milovanpms/tictac/assets/images/block_diagram.png

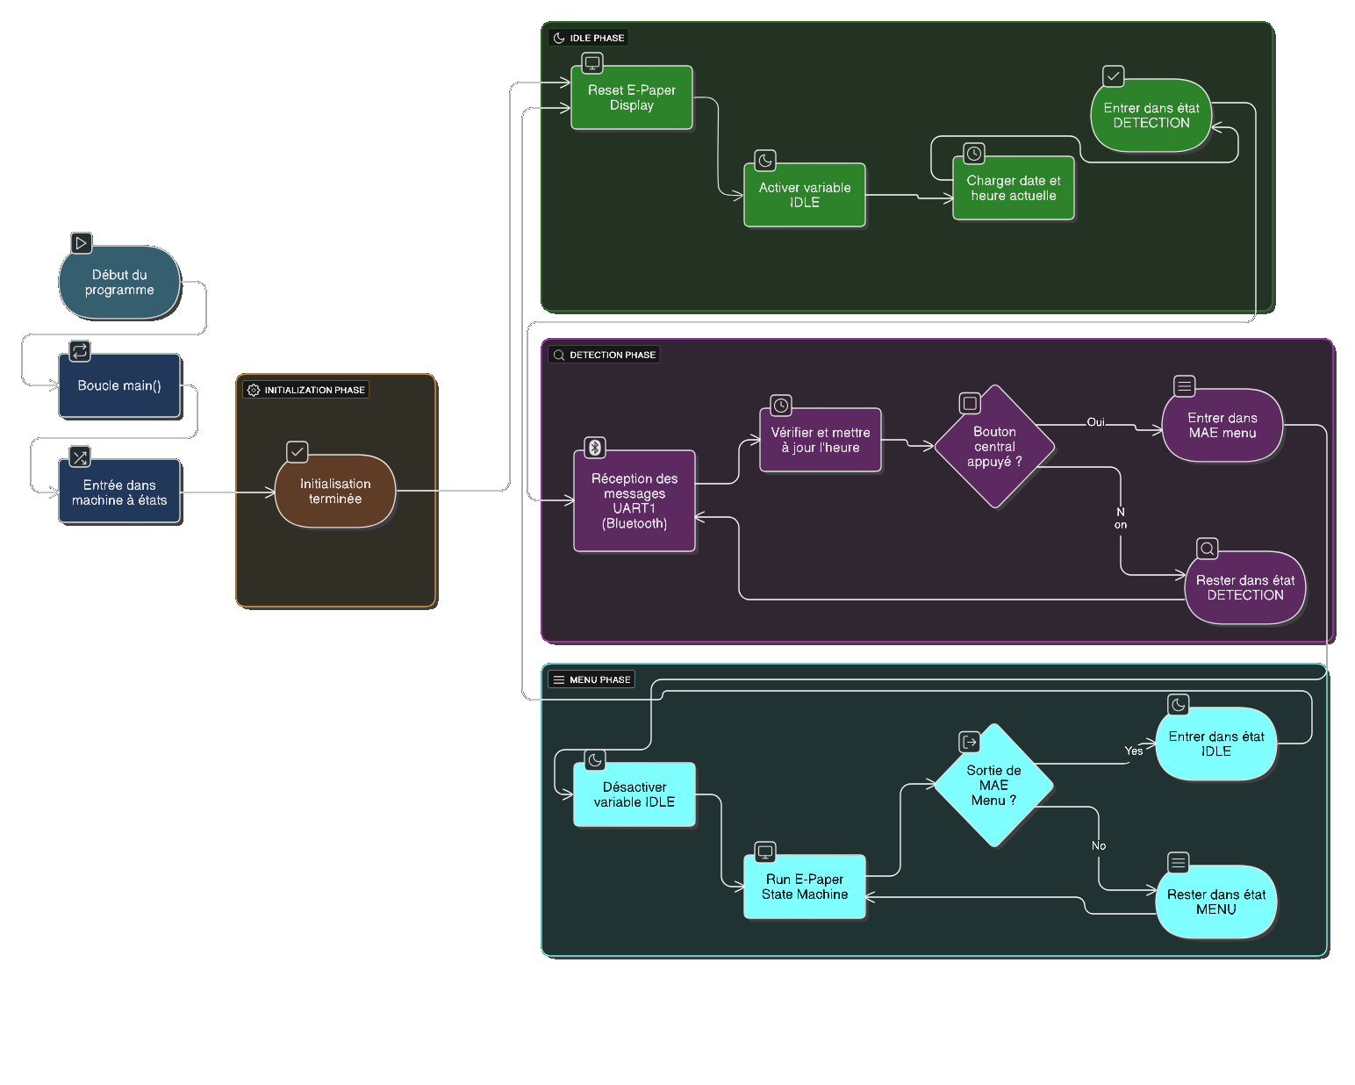
assets/images/block_diagram.png
