milovanpms/tictac/assets/images/croquis.jpg

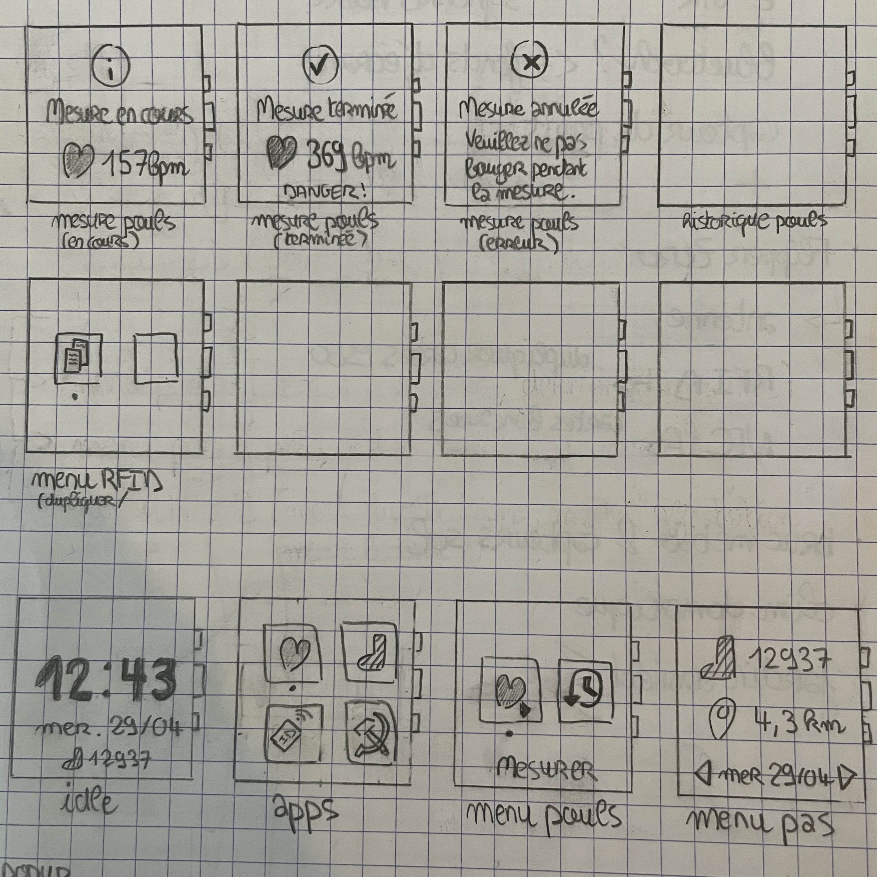
assets/images/croquis.jpg
