milovanpms/tictac/assets/images/photos/IMG_0963.jpg

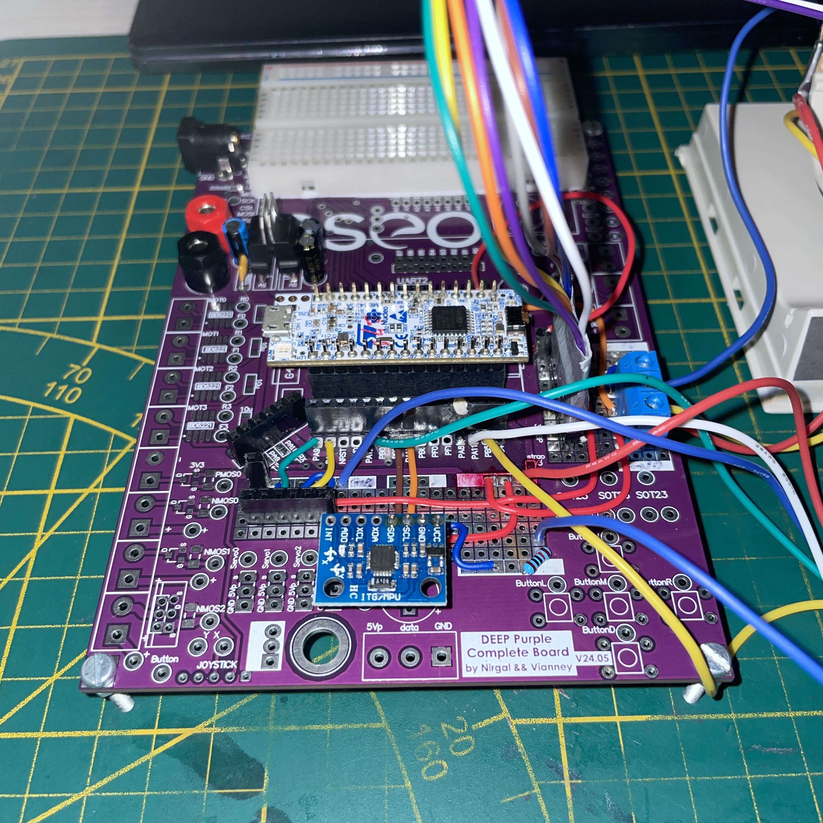
assets/images/photos/IMG_0963.jpg
