milovanpms/tictac/assets/images/photos/IMG_0964.jpg

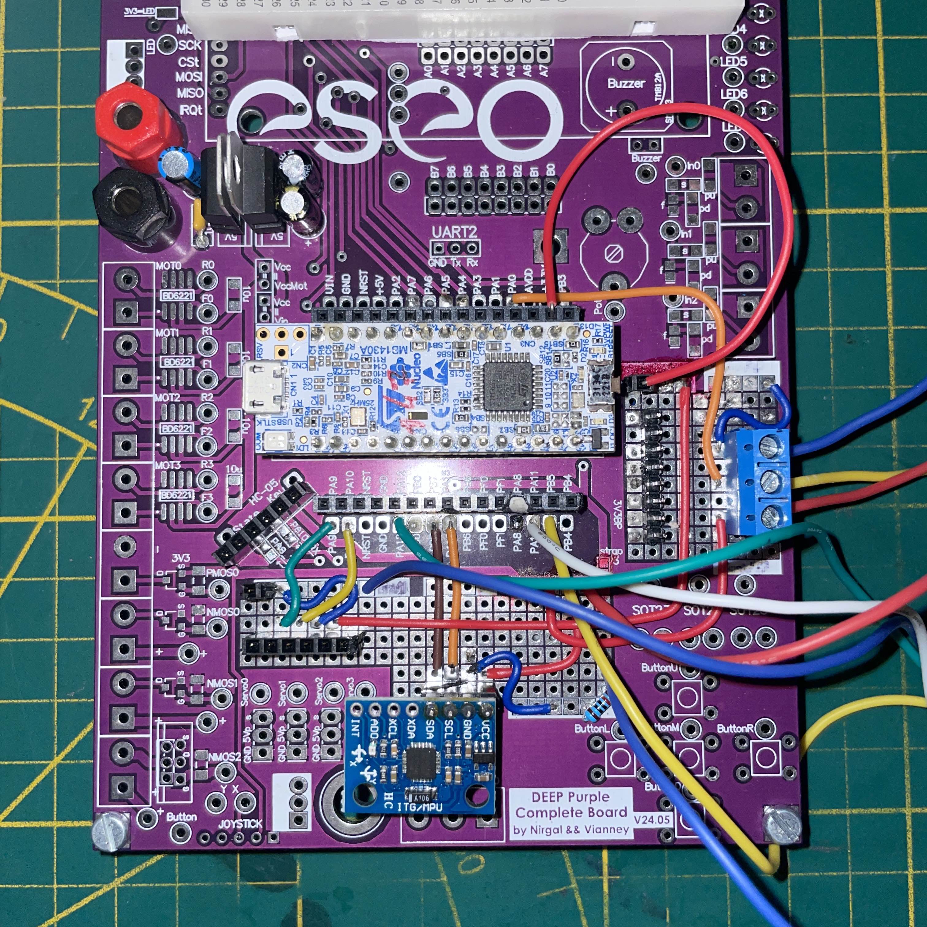
assets/images/photos/IMG_0964.jpg
