milovanpms/tictac/assets/images/photos/IMG_0965.jpg

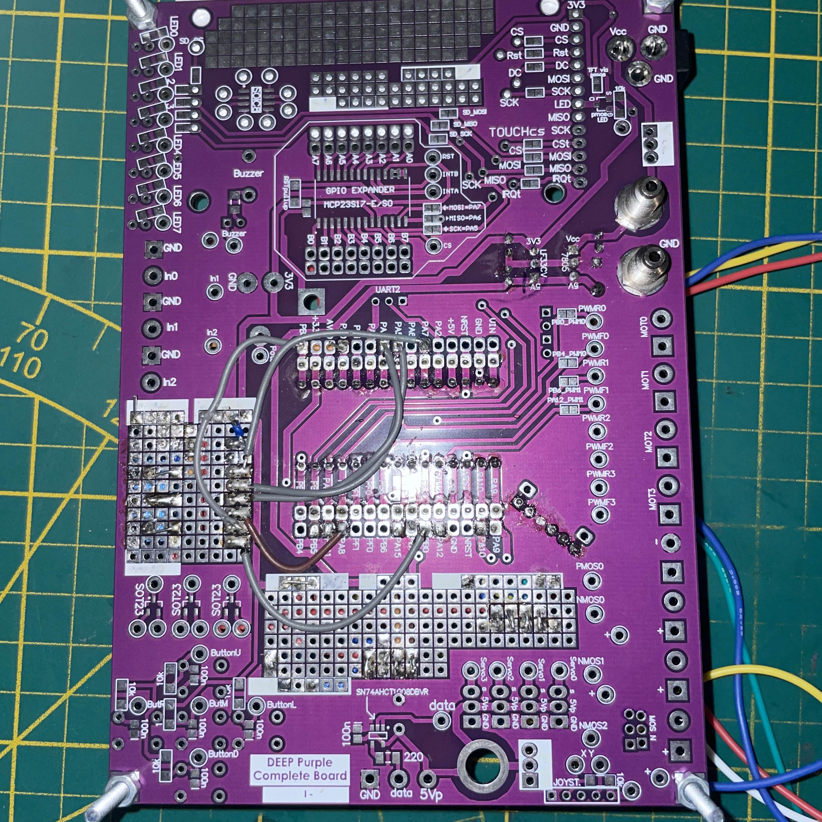
assets/images/photos/IMG_0965.jpg
