milovanpms/tictac/firmware/app/epaper/epaper_bitmaps.h

/**
 * @file epaper_bitmaps.h
 * @author Milovan Paget
 * @brief Définition des données bitmap pour l'affichage des icônes
 */

#include <stdlib.h>

extern const unsigned char image[];

/**
 * @brief Tableau de données bitmap pour l'icône cadre
 *
 */
static const uint8_t cadre[343] = {
    // ∙∙∙∙∙∙∙∙∙∙∙∙∙∙∙∙∙∙∙∙∙∙∙∙∙∙∙∙∙∙∙∙∙∙∙∙∙∙∙∙∙∙∙∙∙∙∙∙∙
    // ∙∙∙∙∙∙∙∙∙∙∙∙∙∙∙∙∙∙∙∙∙∙∙∙∙∙∙∙∙∙∙∙∙∙∙∙∙∙∙∙∙∙∙∙∙∙∙∙∙
    // ∙∙∙∙∙∙∙∙∙∙∙∙∙∙∙∙∙∙█████████████∙∙∙∙∙∙∙∙∙∙∙∙∙∙∙∙∙∙
    // ∙∙∙∙∙∙∙∙∙∙∙∙∙∙∙∙∙∙█████████████∙∙∙∙∙∙∙∙∙∙∙∙∙∙∙∙∙∙
    // ∙∙∙∙∙∙∙∙∙∙∙∙∙∙█████████████████████∙∙∙∙∙∙∙∙∙∙∙∙∙∙
    // ∙∙∙∙∙∙∙∙∙∙∙∙∙∙█████████████████████∙∙∙∙∙∙∙∙∙∙∙∙∙∙
    // ∙∙∙∙∙∙∙∙∙∙█████████∙∙∙∙∙∙∙∙∙∙∙█████████∙∙∙∙∙∙∙∙∙∙
    // ∙∙∙∙∙∙∙∙∙∙█████████∙∙∙∙∙∙∙∙∙∙∙█████████∙∙∙∙∙∙∙∙∙∙
    // ∙∙∙∙∙∙∙∙██████████∙∙∙∙∙∙∙∙∙∙∙∙███████████∙∙∙∙∙∙∙∙
    // ∙∙∙∙∙∙∙∙███████∙∙∙∙∙∙∙∙∙∙∙∙∙∙∙∙∙∙∙███████∙∙∙∙∙∙∙∙
    // ∙∙∙∙∙∙████████∙∙∙∙∙∙∙∙∙∙∙∙∙∙∙∙∙∙∙∙█████████∙∙∙∙∙∙
    // ∙∙∙∙∙∙███████∙∙∙∙∙∙∙∙∙∙∙∙∙∙∙∙∙∙∙∙∙∙∙███████∙∙∙∙∙∙
    // ∙∙∙∙∙∙██████∙∙∙∙∙∙∙∙∙∙∙∙∙∙∙∙∙∙∙∙∙∙∙∙███████∙∙∙∙∙∙
    // ∙∙∙∙∙∙█████∙∙∙∙∙∙∙∙∙∙∙∙∙∙∙∙∙∙∙∙∙∙∙∙∙∙∙█████∙∙∙∙∙∙
    // ∙∙∙∙██████∙∙∙∙∙∙∙∙∙∙∙∙∙∙∙∙∙∙∙∙∙∙∙∙∙∙∙∙███████∙∙∙∙
    // ∙∙∙∙█████∙∙∙∙∙∙∙∙∙∙∙∙∙∙∙∙∙∙∙∙∙∙∙∙∙∙∙∙∙∙∙█████∙∙∙∙
    // ∙∙∙∙█████∙∙∙∙∙∙∙∙∙∙∙∙∙∙∙∙∙∙∙∙∙∙∙∙∙∙∙∙∙∙∙█████∙∙∙∙
    // ∙∙∙∙█████∙∙∙∙∙∙∙∙∙∙∙∙∙∙∙∙∙∙∙∙∙∙∙∙∙∙∙∙∙∙∙█████∙∙∙∙
    // ∙∙██████∙∙∙∙∙∙∙∙∙∙∙∙∙∙∙∙∙∙∙∙∙∙∙∙∙∙∙∙∙∙∙∙███████∙∙
    // ∙∙████∙∙∙∙∙∙∙∙∙∙∙∙∙∙∙∙∙∙∙∙∙∙∙∙∙∙∙∙∙∙∙∙∙∙∙∙█████∙∙
    // ∙∙████∙∙∙∙∙∙∙∙∙∙∙∙∙∙∙∙∙∙∙∙∙∙∙∙∙∙∙∙∙∙∙∙∙∙∙∙█████∙∙
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
    0xfc, 0x00, 0x00, 0x00, 0x00, 0x00, 0xfc,
    0xfc, 0x00, 0x00, 0x00, 0x00, 0x00, 0xfc,
    0xfc, 0x00, 0x00, 0x00, 0x00, 0x00, 0xfc,
    0xfc, 0x00, 0x00, 0x00, 0x00, 0x00, 0xfc,
    0xfc, 0x00, 0x00, 0x00, 0x00, 0x00, 0xfc,
    0xfc, 0x00, 0x00, 0x00, 0x00, 0x00, 0xfc,
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
};

/**
 * @brief Tableau de données bitmap pour l'icône satellite
 *
 */
static const uint8_t satellite[120] = {
    // ∙∙∙∙∙∙∙█████∙∙∙∙∙∙∙∙∙∙∙∙∙∙∙∙∙∙
    // ∙∙∙∙████████∙∙∙∙∙∙∙∙∙∙∙∙∙∙∙∙∙∙
    // ∙∙∙█████∙∙∙∙∙∙∙∙∙∙∙∙∙∙∙████∙∙∙
    // ∙∙███∙∙∙∙∙∙∙∙∙∙∙∙∙∙∙∙∙██████∙∙
    // ∙████∙∙███∙∙∙∙∙∙∙∙∙∙∙████████∙
    // ∙██∙∙█████∙∙∙∙∙∙∙∙∙∙██████████
    // ∙██∙∙███∙∙∙∙∙∙∙∙∙∙∙∙███∙██∙███
    // ███∙███∙∙∙█████∙∙∙████████████
    // ██∙∙██∙∙████████∙█████████████
    // ██∙∙██∙∙████∙∙██∙███∙██∙██∙███
    // ██∙∙∙∙∙███∙∙█████████████████∙
    // ██∙∙∙∙∙███∙██████████████████∙
    // ∙∙∙∙∙∙∙██∙██████∙███████████∙∙
    // ∙∙∙∙∙∙∙██∙█████∙∙∙████████∙∙∙∙
    // ∙∙∙∙∙∙∙████████∙∙∙████████∙∙∙∙
    // ∙∙∙∙∙∙∙∙█████∙∙∙∙∙∙∙█████∙∙∙∙∙
    // ∙∙∙∙∙∙∙∙∙∙██∙∙∙∙∙∙∙∙∙██∙∙∙∙∙∙∙
    // ∙∙∙∙∙∙∙∙█████∙∙∙∙∙∙∙∙████∙∙∙∙∙
    // ∙∙∙∙∙∙∙████████∙∙∙∙∙██████∙∙∙∙
    // ∙∙∙∙∙∙∙████████∙∙∙∙∙██∙∙██∙∙∙∙
    // ∙∙∙∙∙████∙██████∙∙∙∙∙██∙████∙∙
    // ∙∙∙∙██████████████∙∙∙███████∙∙
    // ∙∙∙████████████████∙∙███████∙∙
    // ∙∙████∙██∙██████∙██∙∙█████∙∙∙∙
    // ∙∙██████████████∙█████████∙∙∙∙
    // ∙∙█████████████∙∙∙███████∙∙∙∙∙
    // ∙∙████∙██∙███∙∙∙∙∙∙∙███∙∙∙∙∙∙∙
    // ∙∙∙██████████∙∙∙∙∙∙∙███∙∙∙∙∙∙∙
    // ∙∙∙∙████████∙∙∙∙∙∙∙∙∙∙∙∙∙∙∙∙∙∙
    // ∙∙∙∙∙█████∙∙∙∙∙∙∙∙∙∙∙∙∙∙∙∙∙∙∙∙
    0x01, 0xf0, 0x00, 0x00,
    0x0f, 0xf0, 0x00, 0x00,
    0x1f, 0x00, 0x01, 0xe0,
    0x38, 0x00, 0x03, 0xf0,
    0x79, 0xc0, 0x07, 0xf8,
    0x67, 0xc0, 0x0f, 0xfc,
    0x67, 0x00, 0x0e, 0xdc,
    0xee, 0x3e, 0x3f, 0xfc,
    0xcc, 0xff, 0x7f, 0xfc,
    0xcc, 0xf3, 0x76, 0xdc,
    0xc1, 0xcf, 0xff, 0xf8,
    0xc1, 0xdf, 0xff, 0xf8,
    0x01, 0xbf, 0x7f, 0xf0,
    0x01, 0xbe, 0x3f, 0xc0,
    0x01, 0xfe, 0x3f, 0xc0,
    0x00, 0xf8, 0x0f, 0x80,
    0x00, 0x30, 0x06, 0x00,
    0x00, 0xf8, 0x07, 0x80,
    0x01, 0xfe, 0x0f, 0xc0,
    0x01, 0xfe, 0x0c, 0xc0,
    0x07, 0xbf, 0x06, 0xf0,
    0x0f, 0xff, 0xc7, 0xf0,
    0x1f, 0xff, 0xe7, 0xf0,
    0x3d, 0xbf, 0x67, 0xc0,
    0x3f, 0xff, 0x7f, 0xc0,
    0x3f, 0xfe, 0x3f, 0x80,
    0x3d, 0xb8, 0x0e, 0x00,
    0x1f, 0xf8, 0x0e, 0x00,
    0x0f, 0xf0, 0x00, 0x00,
    0x07, 0xc0, 0x00, 0x00
};

/**
 * @brief Tableau de données bitmap pour l'icône plume
 *
 */
static const uint8_t plume[120] = {
    // ∙∙∙∙∙∙∙∙∙∙∙∙∙∙∙∙∙∙∙∙█████████∙
    // ∙∙∙∙∙∙∙∙∙∙∙∙∙∙∙∙∙████████████∙
    // ∙∙∙∙∙∙∙∙∙∙∙∙∙∙∙███████∙∙████∙∙
    // ∙∙∙∙∙∙∙∙∙∙∙∙∙∙∙███∙∙██∙∙██∙∙∙∙
    // ∙∙∙∙∙∙∙∙∙∙∙∙∙∙███∙████████∙∙∙∙
    // ∙∙∙∙∙∙∙∙∙∙∙∙∙███∙███∙████∙∙∙∙∙
    // ∙∙∙∙∙∙∙∙∙∙∙∙███∙∙██∙∙██∙∙∙∙∙∙∙
    // ∙∙∙∙∙∙∙∙∙∙∙████████∙███∙∙∙∙∙∙∙
    // ∙∙∙∙∙∙∙∙∙∙∙██∙████∙∙██∙∙∙∙∙∙∙∙
    // ∙∙∙∙∙∙∙∙∙∙∙██∙██∙∙∙∙██∙∙∙∙∙∙∙∙
    // ∙∙∙∙∙∙∙∙∙∙█████∙∙∙██∙∙∙∙∙∙∙∙∙∙
    // ∙∙∙∙∙∙∙∙∙∙██████████∙∙∙∙∙∙∙∙∙∙
    // ∙∙∙∙∙∙∙∙∙∙█████████∙∙∙∙∙∙∙∙∙∙∙
    // ∙∙∙∙∙∙∙∙∙∙██████∙∙∙∙∙∙∙∙∙∙∙∙∙∙
    // ∙∙∙∙∙∙∙∙████████∙∙∙∙∙∙∙∙∙∙∙∙∙∙
    // ∙∙∙∙∙∙∙∙██∙∙∙∙∙∙∙∙∙∙∙∙∙∙∙∙∙∙∙∙
    // ∙∙∙∙∙∙∙∙██∙∙∙∙∙∙∙∙∙∙∙∙∙∙∙∙∙∙∙∙
    // ∙∙∙∙███████████∙∙∙∙∙∙∙∙∙∙∙∙∙∙∙
    // ∙∙∙∙███████████∙∙∙∙∙∙∙∙∙∙∙∙∙∙∙
    // ∙∙∙∙∙███∙∙∙██∙∙∙∙∙∙∙∙∙∙∙∙∙∙∙∙∙
    // ∙∙∙∙∙███∙∙∙██∙∙∙∙∙∙∙∙∙∙∙∙∙∙∙∙∙
    // ∙∙██████∙∙∙█████∙∙∙∙∙∙∙∙∙∙∙∙∙∙
    // ∙████████∙∙∙█████∙∙∙∙∙∙∙∙∙∙∙∙∙
    // ∙████████∙∙∙∙∙∙███∙∙∙∙∙∙∙∙∙∙∙∙
    // ∙█████████████████∙∙∙∙∙∙∙∙∙∙∙∙
    // ∙█████████████████∙∙∙∙∙∙∙∙∙∙∙∙
    // ∙█████████████████∙∙∙∙∙∙∙∙∙∙∙∙
    // ∙█████████████████∙∙∙∙∙∙∙∙∙∙∙∙
    // ∙█████████████████∙∙∙∙∙∙∙∙∙∙∙∙
    // ∙∙██████████████∙∙∙∙∙∙∙∙∙∙∙∙∙∙
    0x00, 0x00, 0x0f, 0xf8,
    0x00, 0x00, 0x7f, 0xf8,
    0x00, 0x01, 0xfc, 0xf0,
    0x00, 0x01, 0xcc, 0xc0,
    0x00, 0x03, 0xbf, 0xc0,
    0x00, 0x07, 0x77, 0x80,
    0x00, 0x0e, 0x66, 0x00,
    0x00, 0x1f, 0xee, 0x00,
    0x00, 0x1b, 0xcc, 0x00,
    0x00, 0x1b, 0x0c, 0x00,
    0x00, 0x3e, 0x30, 0x00,
    0x00, 0x3f, 0xf0, 0x00,
    0x00, 0x3f, 0xe0, 0x00,
    0x00, 0x3f, 0x00, 0x00,
    0x00, 0xff, 0x00, 0x00,
    0x00, 0xc0, 0x00, 0x00,
    0x00, 0xc0, 0x00, 0x00,
    0x0f, 0xfe, 0x00, 0x00,
    0x0f, 0xfe, 0x00, 0x00,
    0x07, 0x18, 0x00, 0x00,
    0x07, 0x18, 0x00, 0x00,
    0x3f, 0x1f, 0x00, 0x00,
    0x7f, 0x8f, 0x80, 0x00,
    0x7f, 0x81, 0xc0, 0x00,
    0x7f, 0xff, 0xc0, 0x00,
    0x7f, 0xff, 0xc0, 0x00,
    0x7f, 0xff, 0xc0, 0x00,
    0x7f, 0xff, 0xc0, 0x00,
    0x7f, 0xff, 0xc0, 0x00,
    0x3f, 0xff, 0x00, 0x00
};

/**
 * @brief Tableau de données bitmap pour l'icône mrnote
 *
 */
static const uint8_t mrnote[120] = {
    // ∙∙∙∙∙∙∙∙∙∙∙∙██∙∙██∙∙███∙∙∙∙∙∙∙
    // ∙∙∙∙∙∙∙∙∙██████████████████∙∙∙
    // ∙∙∙∙∙∙∙∙████████████████████∙∙
    // ∙∙∙∙∙∙∙███∙∙██∙∙██∙∙████████∙∙
    // ∙∙∙∙∙∙∙███∙∙██∙∙██∙∙██∙███████
    // ∙∙∙∙∙∙████∙∙∙∙∙∙∙∙∙∙∙∙███∙████
    // ∙∙∙∙∙∙██∙∙∙∙∙∙∙∙∙∙∙∙∙∙██∙∙████
    // ∙∙∙∙∙∙██∙∙∙∙∙∙∙∙∙∙∙∙∙∙██∙∙████
    // ∙∙∙∙∙███∙∙███∙∙██∙∙∙████∙∙████
    // ∙∙∙∙∙██∙∙∙███∙∙██∙∙∙███∙∙∙████
    // ∙∙∙∙∙██∙∙∙∙∙∙∙∙∙∙∙∙∙█████∙████
    // ∙∙∙████∙∙██∙∙∙∙██∙∙██████∙████
    // ∙∙∙██∙∙∙∙████████∙∙██∙∙∙∙∙████
    // ∙∙∙██∙∙∙∙∙█████∙∙∙∙██∙∙∙∙∙████
    // ∙∙███∙∙∙∙∙█████∙∙████████∙████
    // ∙∙██∙∙∙∙∙∙∙∙∙∙∙∙∙████████∙████
    // ∙∙██∙∙∙∙∙∙∙∙∙∙∙∙∙███∙∙∙∙∙∙████
    // ████∙∙∙∙∙∙∙∙∙∙∙∙████∙∙∙∙∙∙████
    // ███∙∙∙∙∙∙∙∙∙∙∙∙∙█████████∙████
    // ███∙∙∙∙∙∙∙∙∙∙∙∙∙█████████∙████
    // ∙∙███████████████∙∙∙∙∙∙∙∙∙████
    // ∙∙███████████████∙∙∙∙∙∙∙∙∙████
    // ∙∙∙∙∙∙∙∙∙██∙█████████████∙████
    // ∙∙∙∙∙∙∙∙∙██∙█████████████∙████
    // ∙∙∙∙∙∙∙∙∙██∙█████████████∙████
    // ∙∙∙∙∙∙∙∙∙██∙∙∙∙∙∙∙∙∙∙∙∙∙∙∙████
    // ∙∙∙∙∙∙∙∙∙██∙∙∙∙∙∙∙∙∙∙∙∙∙∙∙████
    // ∙∙∙∙∙∙∙∙∙██∙∙∙∙∙∙∙∙∙∙∙∙∙∙∙████
    // ∙∙∙∙∙∙∙∙∙█████████████████████
    // ∙∙∙∙∙∙∙∙∙∙██████████████████∙∙
    0x00, 0x0c, 0xce, 0x00,
    0x00, 0x7f, 0xff, 0xe0,
    0x00, 0xff, 0xff, 0xf0,
    0x01, 0xcc, 0xcf, 0xf0,
    0x01, 0xcc, 0xcd, 0xfc,
    0x03, 0xc0, 0x03, 0xbc,
    0x03, 0x00, 0x03, 0x3c,
    0x03, 0x00, 0x03, 0x3c,
    0x07, 0x39, 0x8f, 0x3c,
    0x06, 0x39, 0x8e, 0x3c,
    0x06, 0x00, 0x0f, 0xbc,
    0x1e, 0x61, 0x9f, 0xbc,
    0x18, 0x7f, 0x98, 0x3c,
    0x18, 0x3e, 0x18, 0x3c,
    0x38, 0x3e, 0x7f, 0xbc,
    0x30, 0x00, 0x7f, 0xbc,
    0x30, 0x00, 0x70, 0x3c,
    0xf0, 0x00, 0xf0, 0x3c,
    0xe0, 0x00, 0xff, 0xbc,
    0xe0, 0x00, 0xff, 0xbc,
    0x3f, 0xff, 0x80, 0x3c,
    0x3f, 0xff, 0x80, 0x3c,
    0x00, 0x6f, 0xff, 0xbc,
    0x00, 0x6f, 0xff, 0xbc,
    0x00, 0x6f, 0xff, 0xbc,
    0x00, 0x60, 0x00, 0x3c,
    0x00, 0x60, 0x00, 0x3c,
    0x00, 0x60, 0x00, 0x3c,
    0x00, 0x7f, 0xff, 0xfc,
    0x00, 0x3f, 0xff, 0xf0
};
