milovanpms/tictac/assets/images/photos/IMG_0959.jpg

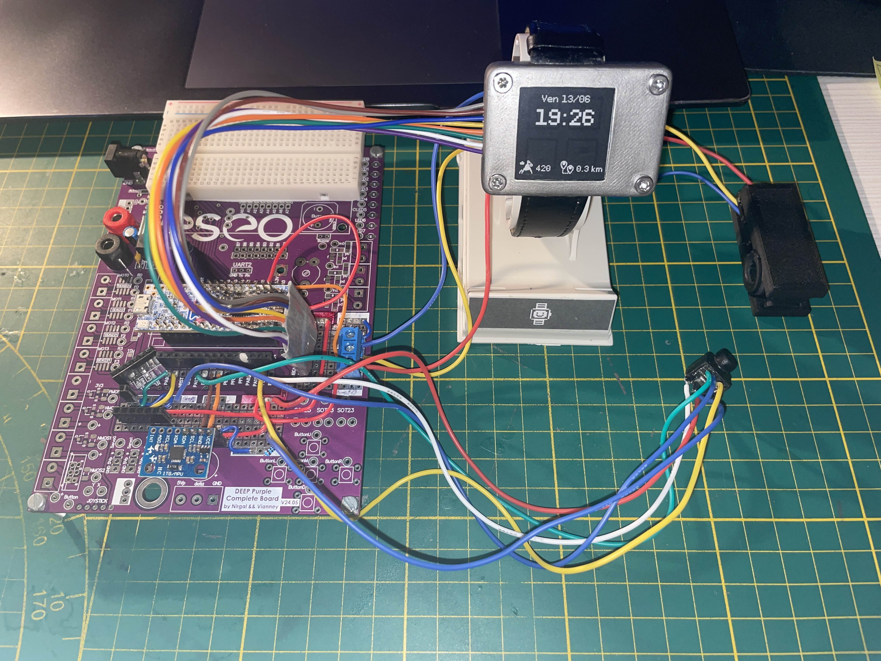
assets/images/photos/IMG_0959.jpg
